SensoriumEmbedded/Internet-Radio/Pictures/stand-alone/20250727_154004.jpg

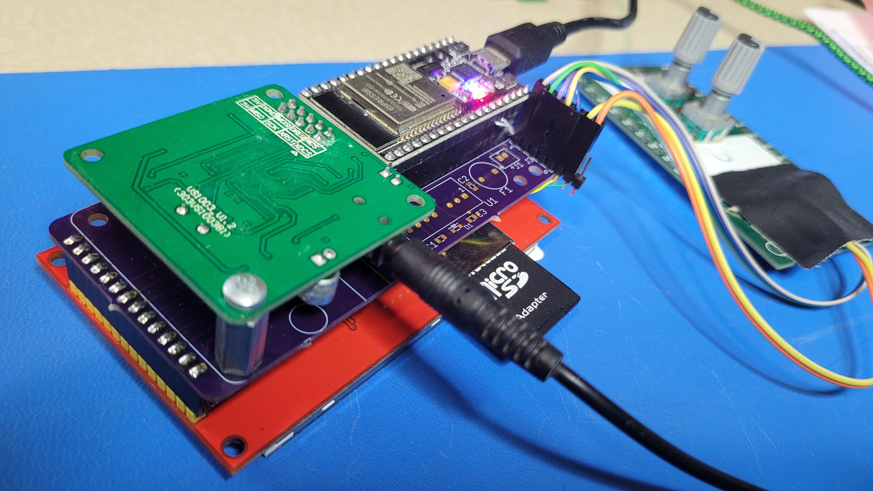
Pictures/stand-alone/20250727_154004.jpg
