SensoriumEmbedded/Internet-Radio/Pictures/stand-alone/20250727_154040.jpg

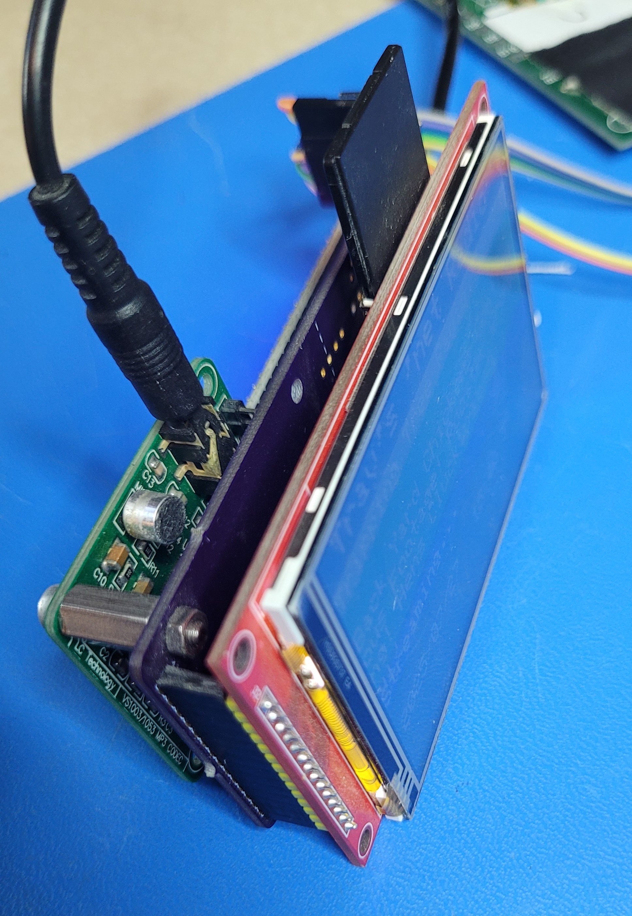
Pictures/stand-alone/20250727_154040.jpg
