SensoriumEmbedded/Internet-Radio/Pictures/stand-alone/20250727_154244.jpg

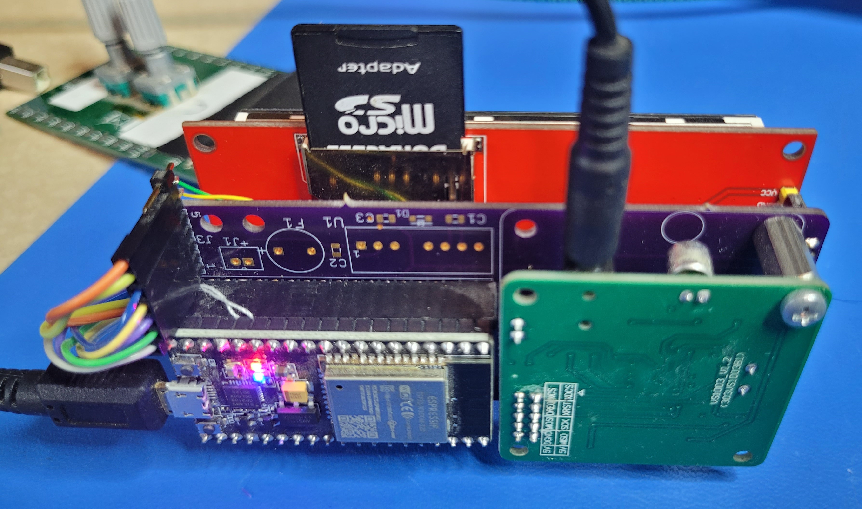
Pictures/stand-alone/20250727_154244.jpg
